HacDC/fenix/firmware/src/fenix/fenix_aprs.rs

// The packet format MUST follow [this protocol document](https://ham.packet-radio.net/packet/aprs-wb2osz/Understanding-APRS-Packets.pdf).

// Will need additional hardware to convert UART -> AFSK 1200bps
