HacDC/fenix/firmware/src/fenix/fenix_beacon.rs

// [This should be a good example to base off of](https://github.com/esp-rs/esp-hal/blob/esp-hal-v1.0.0/examples/wifi/embassy_access_point_with_sta/src/main.rs)

// Should create an AP and host a simple page with the current location
