HacDC/fenix/firmware/misc/i2c_scanner.ino

/* I made this to scan on our specific I2C setup.
   Use Platformio or the arduino IDE with
   https://jihulab.com/esp-mirror/espressif/arduino-esp32.git
*/

#include <Arduino.h>
#ifndef ARDUINO_USB_MODE
#error This ESP32 SoC has no Native USB interface
#elif ARDUINO_USB_MODE == 1
#warning This sketch should be used when USB is in OTG mode
void setup() {}
void loop() {}
#else
#include "USB.h"

#if !ARDUINO_USB_CDC_ON_BOOT
USBCDC USBSerial;
#endif

static void usbEventCallback(void *arg, esp_event_base_t event_base, int32_t event_id, void *event_data) {
  if (event_base == ARDUINO_USB_EVENTS) {
    arduino_usb_event_data_t *data = (arduino_usb_event_data_t *)event_data;
    switch (event_id) {
      case ARDUINO_USB_STARTED_EVENT: Serial.println("USB PLUGGED"); break;
      case ARDUINO_USB_STOPPED_EVENT: Serial.println("USB UNPLUGGED"); break;
      case ARDUINO_USB_SUSPEND_EVENT: Serial.printf("USB SUSPENDED: remote_wakeup_en: %u\n", data->suspend.remote_wakeup_en); break;
      case ARDUINO_USB_RESUME_EVENT:  Serial.println("USB RESUMED"); break;

      default: break;
    }
  } else if (event_base == ARDUINO_USB_CDC_EVENTS) {
    arduino_usb_cdc_event_data_t *data = (arduino_usb_cdc_event_data_t *)event_data;
    switch (event_id) {
      case ARDUINO_USB_CDC_CONNECTED_EVENT:    Serial.println("CDC CONNECTED"); break;
      case ARDUINO_USB_CDC_DISCONNECTED_EVENT: Serial.println("CDC DISCONNECTED"); break;
      case ARDUINO_USB_CDC_LINE_STATE_EVENT:   Serial.printf("CDC LINE STATE: dtr: %u, rts: %u\n", data->line_state.dtr, data->line_state.rts); break;
      case ARDUINO_USB_CDC_LINE_CODING_EVENT:
        Serial.printf(
          "CDC LINE CODING: bit_rate: %lu, data_bits: %u, stop_bits: %u, parity: %u\n", data->line_coding.bit_rate, data->line_coding.data_bits,
          data->line_coding.stop_bits, data->line_coding.parity
        );
        break;
      case ARDUINO_USB_CDC_RX_EVENT:
        Serial.printf("CDC RX [%u]:", data->rx.len);
        {
          uint8_t buf[data->rx.len];
          size_t len = USBSerial.read(buf, data->rx.len);
          Serial.write(buf, len);
        }
        Serial.println();
        break;
      case ARDUINO_USB_CDC_RX_OVERFLOW_EVENT: Serial.printf("CDC RX Overflow of %d bytes", data->rx_overflow.dropped_bytes); break;

      default: break;
    }
  }
}

#include <Wire.h>

// Set I2C bus to use: Wire, Wire1, etc.
#define WIRE Wire

void setup() {
  WIRE.begin(48, 47);

  Serial.begin(9600);
  USB.onEvent(usbEventCallback);
  USBSerial.onEvent(usbEventCallback);

  USBSerial.begin();
  USB.begin();
  while (!Serial)
     delay(10);
  USBSerial.println("\nI2C Scanner");
}


void loop() {
  byte error, address;
  int nDevices;

  USBSerial.println("Scanning...");

  nDevices = 0;
  for(address = 1; address < 127; address++ )
  {
    // The i2c_scanner uses the return value of
    // the Write.endTransmisstion to see if
    // a device did acknowledge to the address.
    WIRE.beginTransmission(address);
    error = WIRE.endTransmission();

    if (error == 0)
    {
      USBSerial.print("I2C device found at address 0x");
      if (address<16)
        USBSerial.print("0");
      USBSerial.print(address,HEX);
      USBSerial.println("  !");
      nDevices++;
    }
    else if (error==4)
    {
      USBSerial.print("Unknown error at address 0x");
      if (address<16)
        USBSerial.print("0");
      USBSerial.println(address,HEX);
    }
  }
  if (nDevices == 0)
    USBSerial.println("No I2C devices found\n");
  else
    USBSerial.println("done\n");

  delay(5000);           // wait 5 seconds for next scan
}

#endif
